friedpies/kelpie-pocket-synth/firmware/src/Kelpie.cpp

#include <Kelpie.h>

Kelpie::Kelpie(bool enableSerial)
{
    if (enableSerial)
    {
        Serial.begin(9600);
    }

    pinMode(SW1, INPUT_PULLUP);
    pinMode(SW2, INPUT_PULLUP);
    pinMode(SW3, INPUT_PULLUP);
    pinMode(SW4, INPUT_PULLUP);

    pinMode(SWLED1, OUTPUT);
    pinMode(SWLED2, OUTPUT);
    pinMode(SWLED3, OUTPUT);
    pinMode(SWLED4, OUTPUT);
}

// this function detects if a knob was changed and returns TRUE if so
pot Kelpie::pollKnobs(bool forceRead)
{
    pot changedPot;
    changedPot.didChange = false;
    for (byte i = 0; i < 16; i++)
    {
        _kelpieKnobs.value[i] = analogRead(_kelpieKnobs.name[i]); // THIS LINE IS BAD

        if ((_kelpieKnobs.value[i] - _kelpieKnobs.state[i]) > 3 || (_kelpieKnobs.value[i] - _kelpieKnobs.state[i]) < -3) // if there is a significant change
        {
            changedPot.didChange = true;
            changedPot.name = i;
            changedPot.value = _kelpieKnobs.value[i];
            _kelpieKnobs.state[i] = _kelpieKnobs.value[i]; //update state
            break;
        }
    }
    return changedPot;
}

int *Kelpie::getKnobs(void)
{
    return _kelpieKnobs.state;
}

boolean Kelpie::pollButtons(void)
{
    boolean didChange = false;
    for (byte i = 0; i < 4; i++)
    {
        if (_kelpieButtons.buttonName[i].update())
        {
            if (_kelpieButtons.buttonName[i].fallingEdge())
            {
                _kelpieButtons.state[i] = !_kelpieButtons.state[i];
                digitalWrite(_kelpieButtons.ledName[i], _kelpieButtons.state[i]);
                didChange = true;
            }
        }
    }
    return didChange;
}

boolean *Kelpie::getButtons(void)
{
    return _kelpieButtons.state;
}
